nathan-cannell/robotic_mice_dxarts/uros_esp32/include/main.h

#ifndef _MAIN_H_
#define _MAIN_H_
#include <Arduino.h>
#include <micro_ros_platformio.h>
#include "dxr_node_common.h"

#if defined(MICRO_ROS_TRANSPORT_ARDUINO_WIFI)
#include <WiFi.h>
#endif

#define OBLED_PIN 2

#endif
